A-Juli/RTEP/Software/MPU6050/MPU6050Register.h

#include <stdint.h>



//accel register addresses
#define OUT_X_accel_m 0x3B
#define OUT_X_accel_l 0x3C
#define OUT_Y_accel_m 0x3D
#define OUT_Y_accel_l 0x3E
#define OUT_Z_accel_m 0x3F
#define OUT_Z_accel_l 0x40

//Temp addresses
#define OUT_Temp_m 0x41
#define OUT_Temp_l 0x42

//gyro register addresses
#define OUT_X_gyro_m 0x43
#define OUT_X_gyro_l 0x44
#define OUT_Y_gyro_m 0x45
#define OUT_Y_gyro_l 0x46
#define OUT_Z_gyro_m 0x47
#define OUT_Z_gyro_l 0x48

#define WHO_AM_I 0x75
