A-Juli/RTEP/Software/ExerciseTests/ExerciseTests.h

#ifndef EXERCISETESTS_H
#define EXERCISETESTS_H

#include <iostream>
#include <math.h>
 
class ExerciseTests
 {
     public:
         //Storage of Accelerometer data for unit test
         double Accel1[3];
         double Accel2[3];
         double Accel3[3];
         double Accel4[3];

         double Angle[10] = {0,0,0,0,0,0,0,0,0,0};
         double DotProduct[10] = {0,0,0,0,0,0,0,0,0,0};
         double TargetAngle[10] = {0,0,0,0,0,0,0,0,0,0};
         double NumAccel = 0;

         ExerciseTests(void);
         double Exercise1(void); 
         double Exercise2(void);

         void Exercise1Setup(void);
         void Exercise2Setup(void);
 };

#endif //EXERCISETESTS_H
